swalt64/IO-Hutschienenboard/DOKU/input_stage_realistic.asc

A1: diffschmtinv
C200: cap; 470n
D200: diode; SMBJ20A
D201: diode; BAS316
L200: ind; 330µ
R1: res; 1K; tol=1 pwr=0.1
R2: res; 10k
R3: res; 10k
R4: res; 10k
R201: res; 3.3k
R202: res; 3.3k
R203: res; 560
U1: PC817C
V1: voltage; 5; Rser=0
V2: voltage; 3.3; Rser=0
V_I01: voltage; SINE(0 11.314 50)
Named nets: 0, Inp1, U1_E, A2_I, U1_K, 5V, 3V3V
.tran 0 200m 0 100u
.model BAS316 D(Is=1e-9 Rs=2 N=1.9 Cjo=2p)
.model SMBJ20A D(Is=1e-12 Rs=0.05 N=1.2 Bv=22 Ibv=1m Cjo=200p)
